aaroncohen73/Reflow-Oven/code/oven.c

/* oven.c - Main loop for reflow oven control and UI
 *
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
 * You should have received a copy of the GNU General Public License
 * along with this program.  If not, see <http://www.gnu.org/licenses/>. */

#include "spi.h"


void oven_init(void)
{
    spi_init();
}

int main(void)
{
    oven_init();

    while (1)
    {
    }

    return 0;
}
